hemangjoshi37a/SWiBoard/Capture2222.PNG

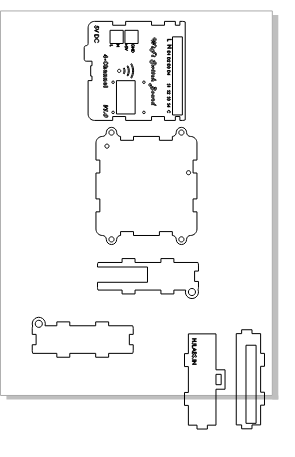
Capture2222.PNG
