hemangjoshi37a/SWiBoard/Capture.PNG

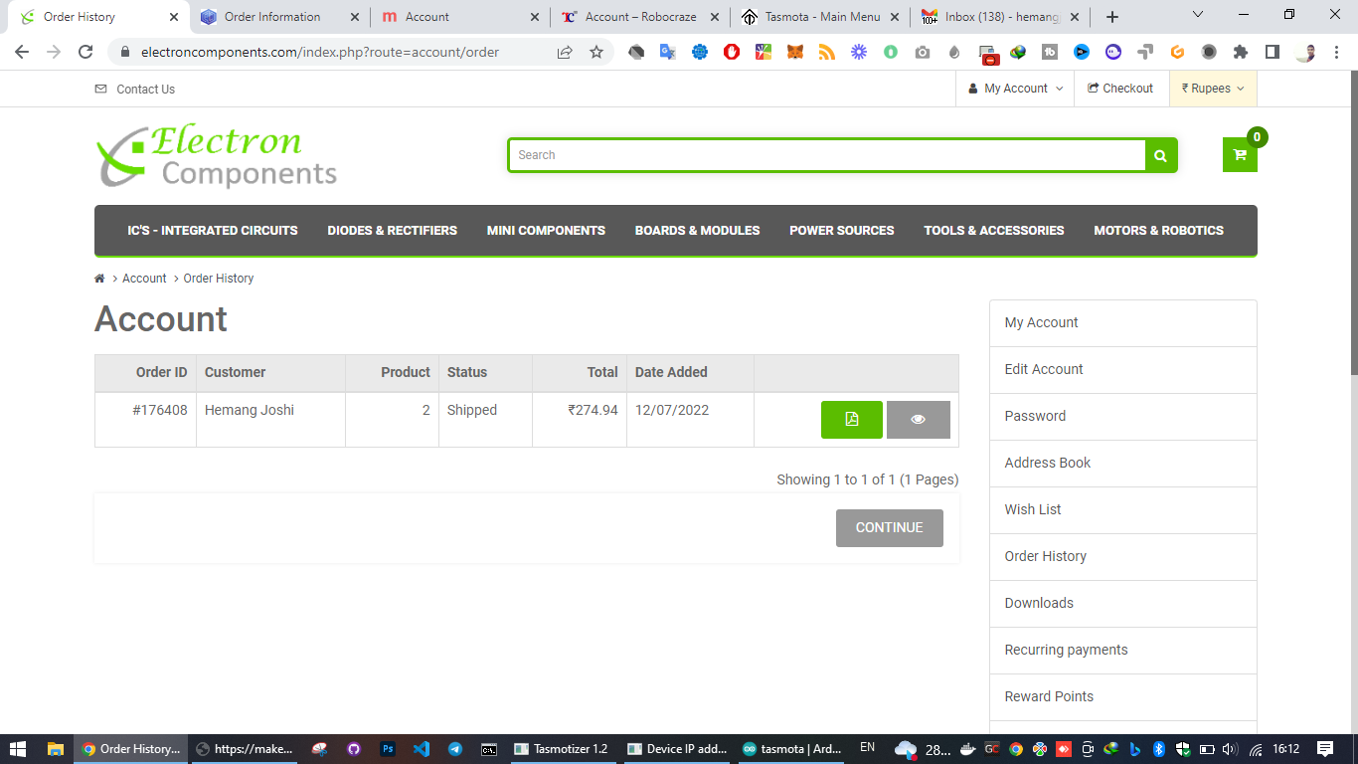
Capture.PNG
