hemangjoshi37a/SWiBoard/Cover_sticker_single.png

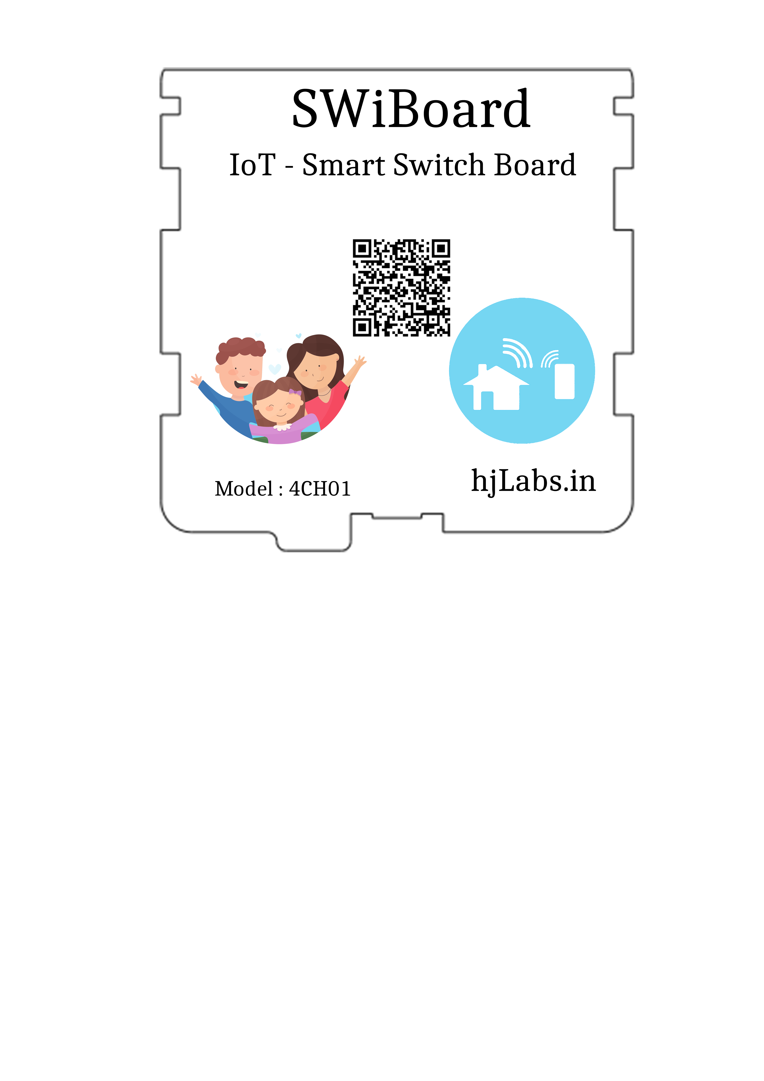
Cover_sticker_single.png
