hemangjoshi37a/SWiBoard/ESP12F_VS_ESP12E.jpg

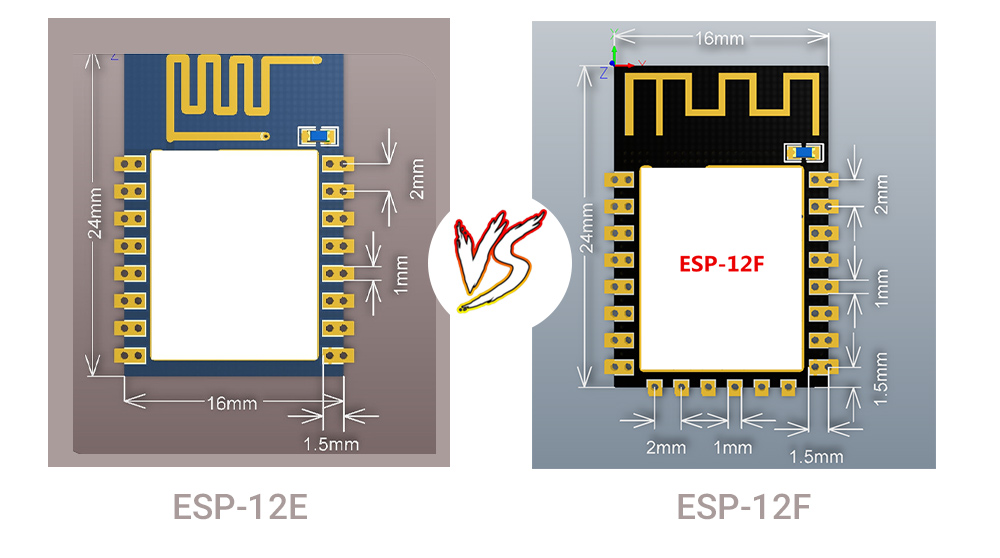
ESP12F_VS_ESP12E.jpg
