hemangjoshi37a/SWiBoard/esp8266_nodeMCU_wifi_switch_pcb_files/AC-Fan-Regulator-Control-Circuit.png

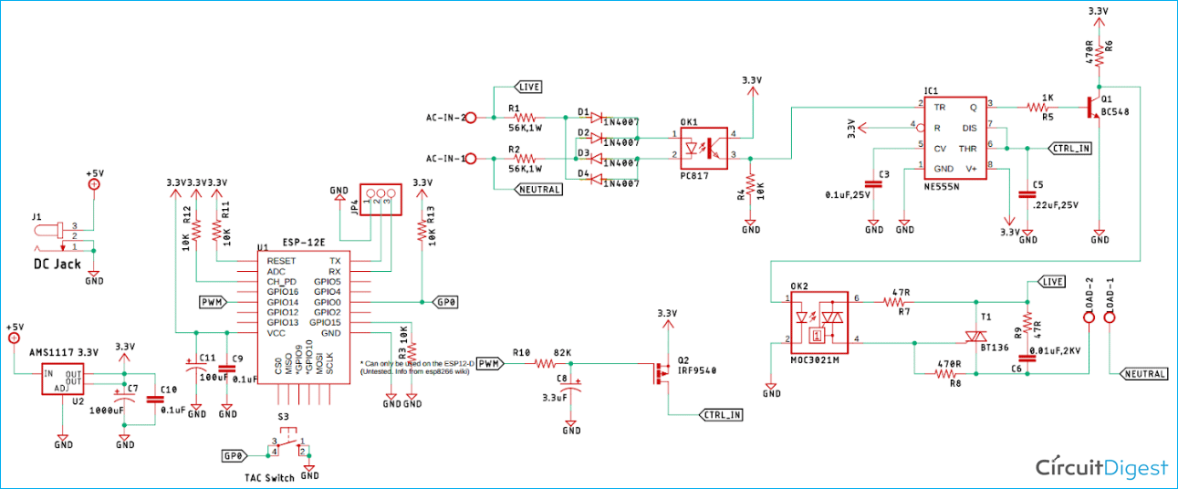
esp8266_nodeMCU_wifi_switch_pcb_files/AC-Fan-Regulator-Control-Circuit.png
