hemangjoshi37a/SWiBoard/flutter_android_app/google_play_dev_console_images/info_graphic_for_playstore.png

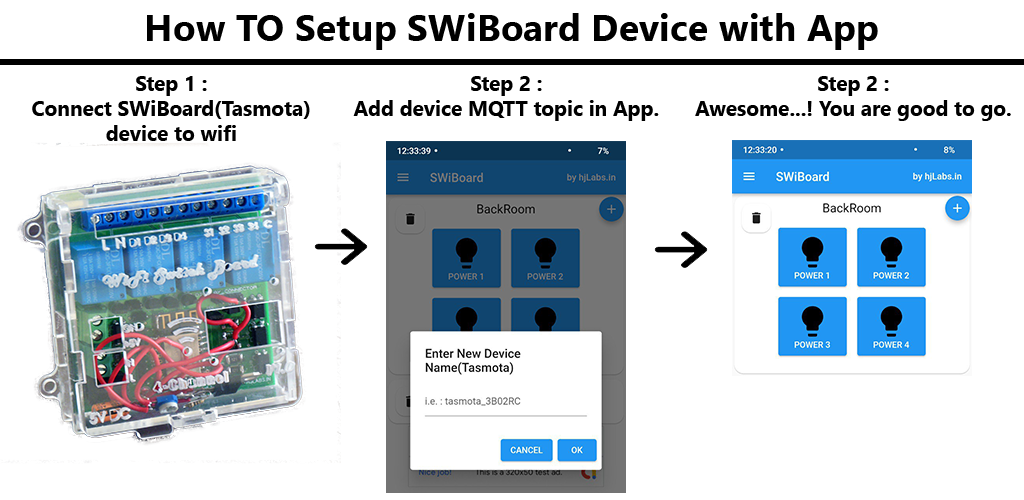
flutter_android_app/google_play_dev_console_images/info_graphic_for_playstore.png
