hemangjoshi37a/SWiBoard/flutter_android_app/google_play_dev_console_images/photo_2022-09-03_09-34-14.jpg

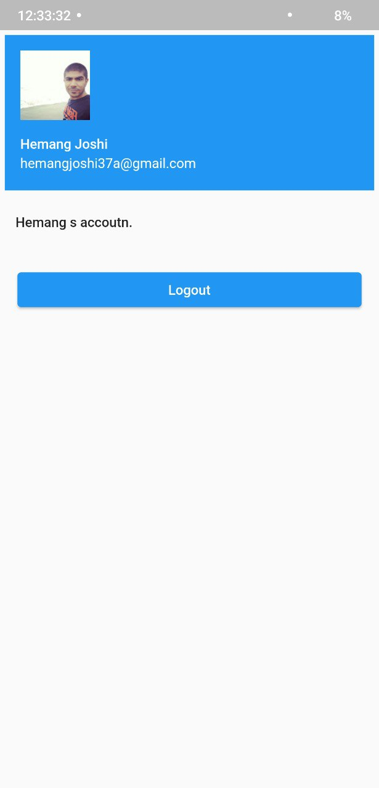
flutter_android_app/google_play_dev_console_images/photo_2022-09-03_09-34-14.jpg
