hemangjoshi37a/SWiBoard/flutter_android_app/google_play_dev_console_images/photo_2022-09-29_00-12-33.jpg

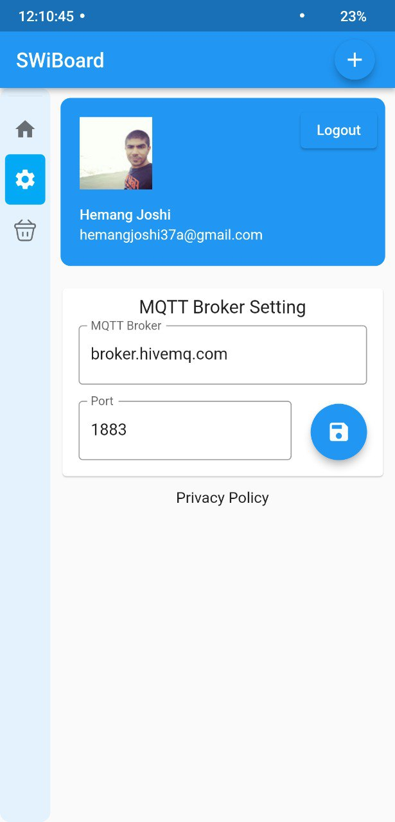
flutter_android_app/google_play_dev_console_images/photo_2022-09-29_00-12-33.jpg
