hemangjoshi37a/SWiBoard/flutter_android_app/google_play_dev_console_images/photo_2022-09-30_11-50-19.jpg

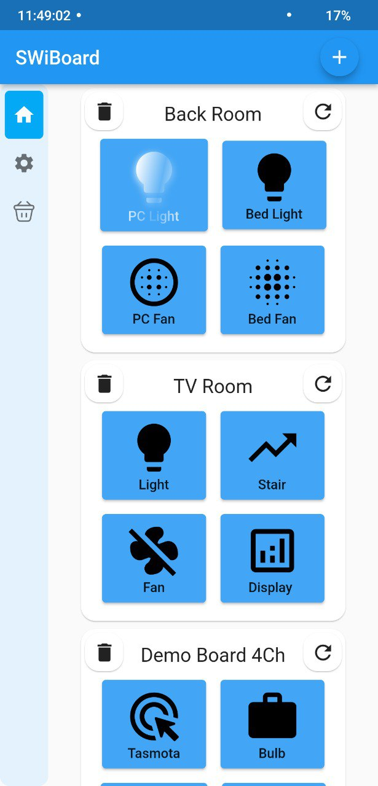
flutter_android_app/google_play_dev_console_images/photo_2022-09-30_11-50-19.jpg
