hemangjoshi37a/SWiBoard/flutter_android_app/google_play_dev_console_images/photo_2022-10-01_15-42-29.jpg

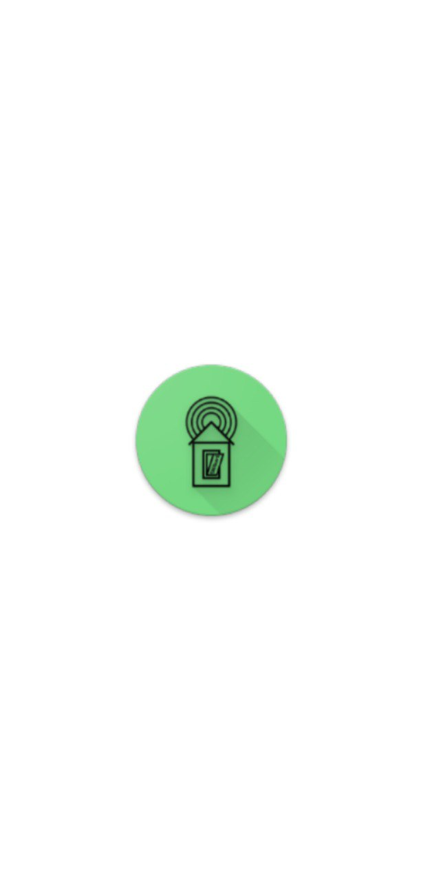
flutter_android_app/google_play_dev_console_images/photo_2022-10-01_15-42-29.jpg
