hemangjoshi37a/SWiBoard/flutter_android_app/google_play_dev_console_images/swiboard_screenshots_combined.png

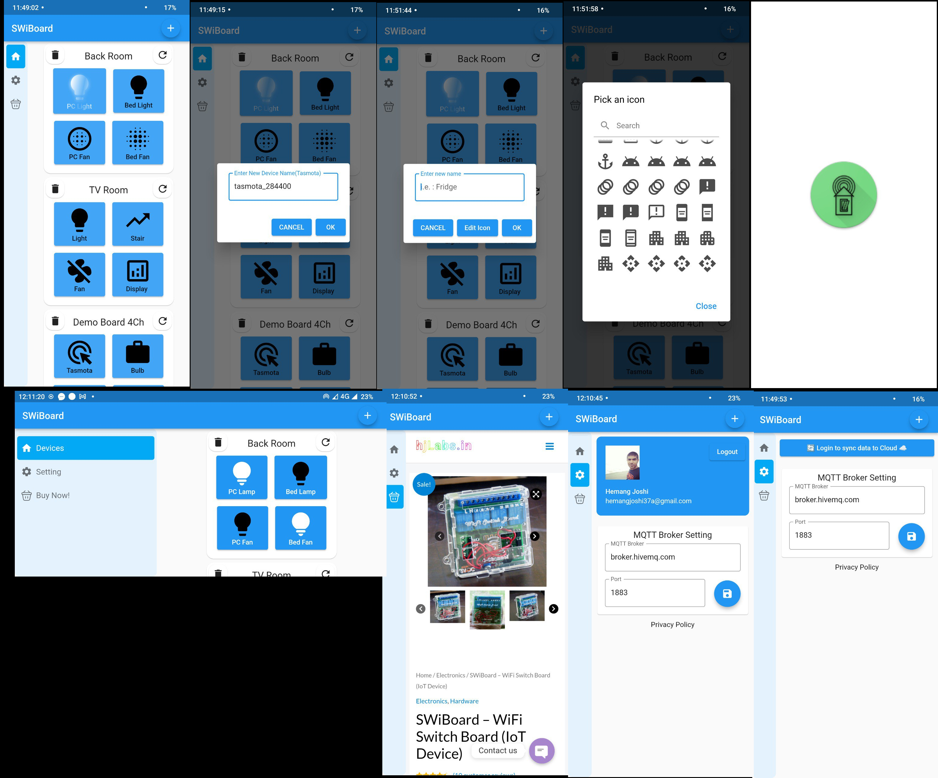
flutter_android_app/google_play_dev_console_images/swiboard_screenshots_combined.png
