hemangjoshi37a/SWiBoard/flutter_android_app/google_play_dev_console_images/tablet_screenshot_image.png

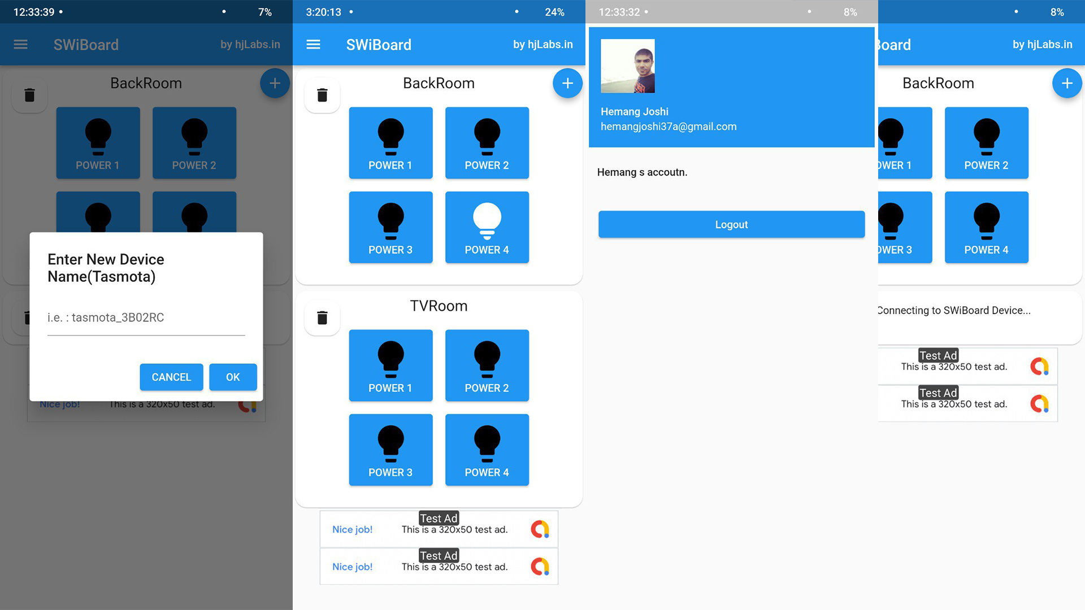
flutter_android_app/google_play_dev_console_images/tablet_screenshot_image.png
