hemangjoshi37a/SWiBoard/Nikon_camera_pics/DSCN5458.JPG

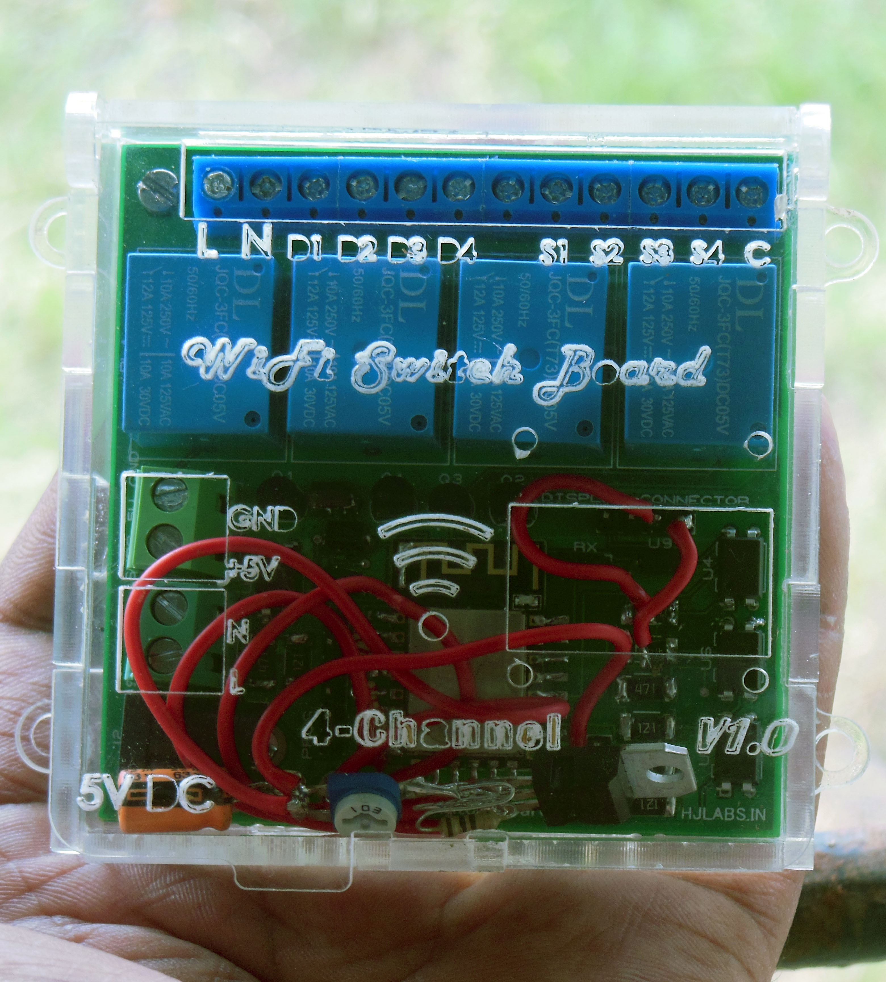
Nikon_camera_pics/DSCN5458.JPG
