hemangjoshi37a/SWiBoard/Nikon_camera_pics/DSCN5459.JPG

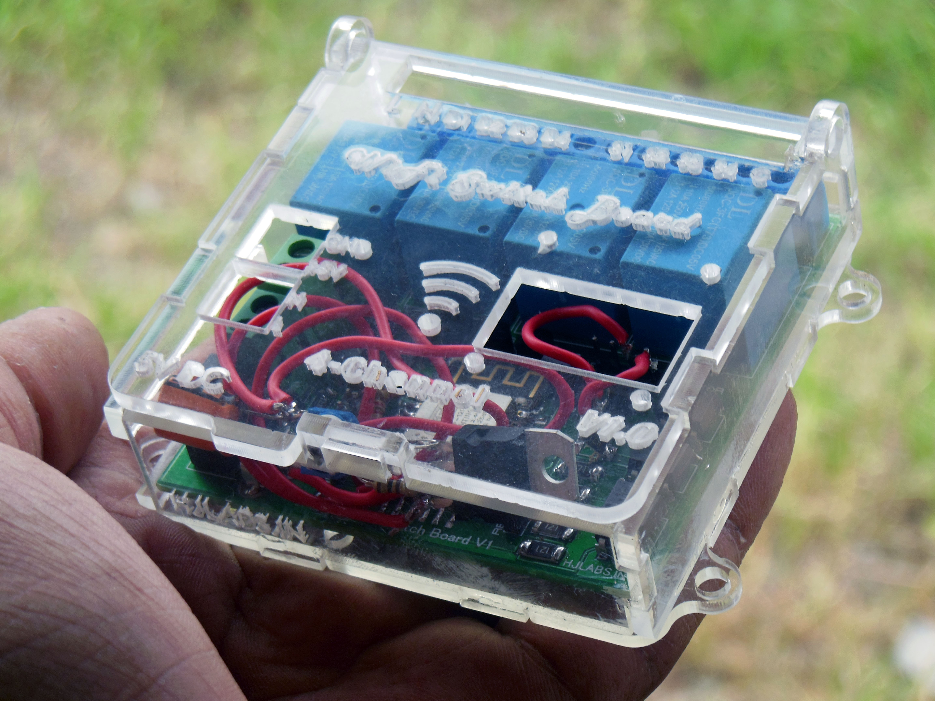
Nikon_camera_pics/DSCN5459.JPG
