hemangjoshi37a/SWiBoard/Nikon_camera_pics/DSCN5460.JPG

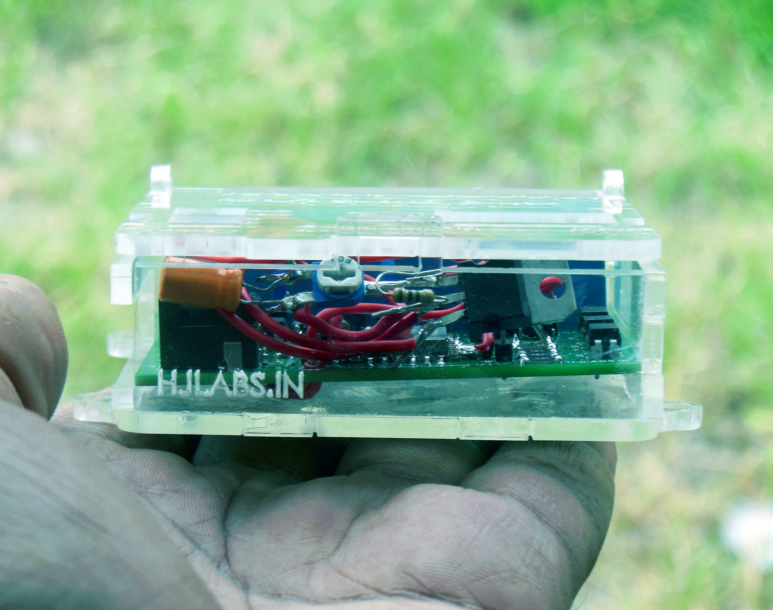
Nikon_camera_pics/DSCN5460.JPG
