hemangjoshi37a/SWiBoard/Nikon_camera_pics/DSCN5461.JPG

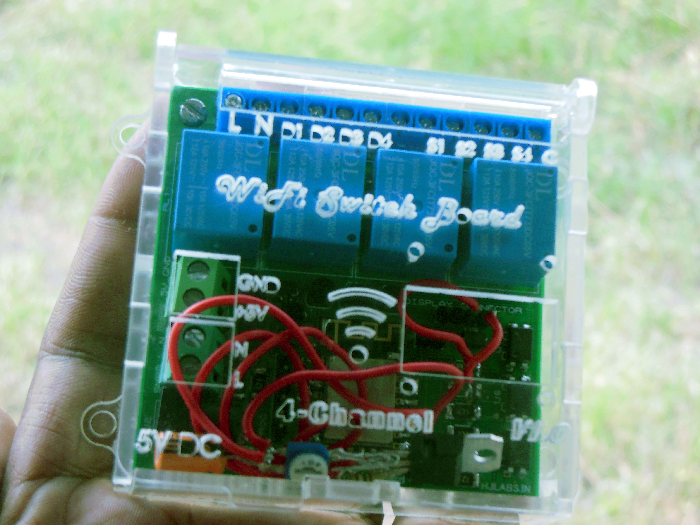
Nikon_camera_pics/DSCN5461.JPG
