hemangjoshi37a/SWiBoard/Nikon_camera_pics/DSCN5462.JPG

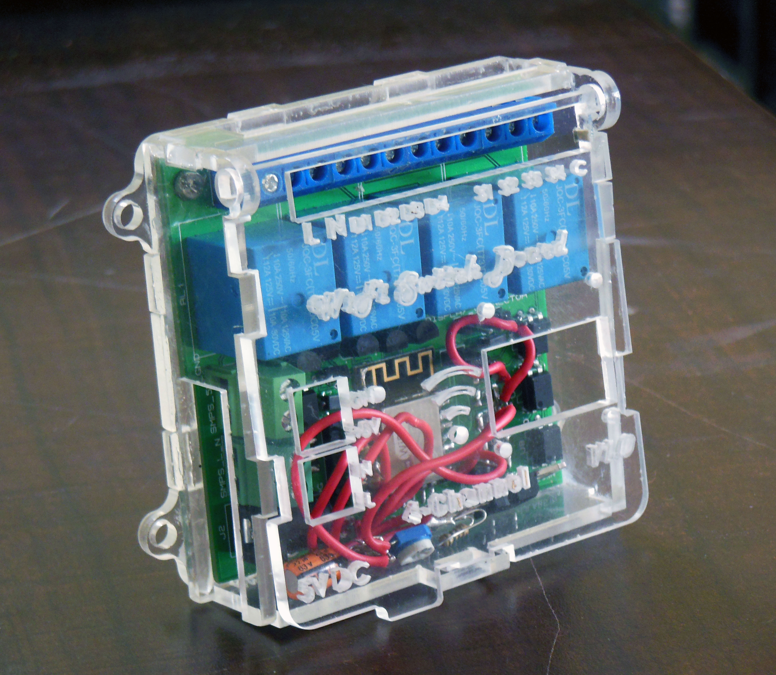
Nikon_camera_pics/DSCN5462.JPG
