hemangjoshi37a/SWiBoard/Nikon_camera_pics/DSCN5463.JPG

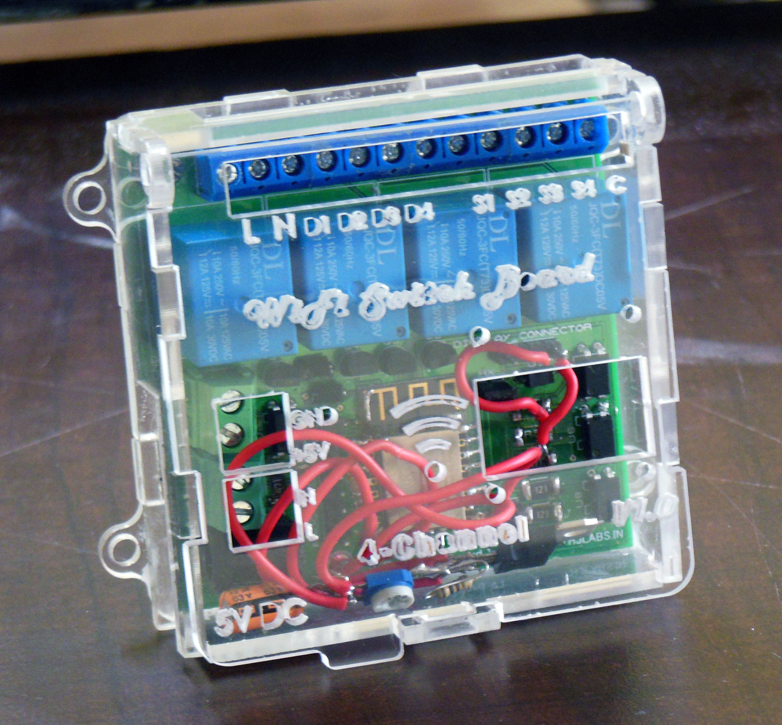
Nikon_camera_pics/DSCN5463.JPG
