hemangjoshi37a/SWiBoard/Nikon_camera_pics/photo_2022-08-03_13-36-46.jpg

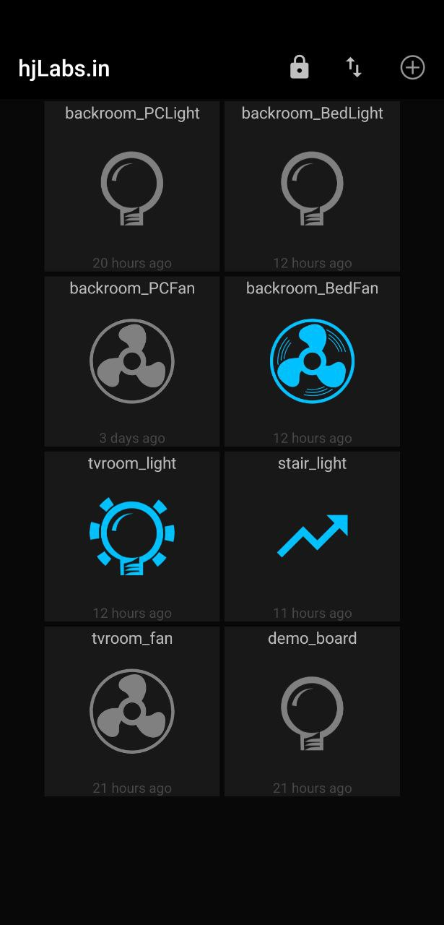
Nikon_camera_pics/photo_2022-08-03_13-36-46.jpg
