hemangjoshi37a/SWiBoard/PCB_FILES/BOX_CAD/render1.png

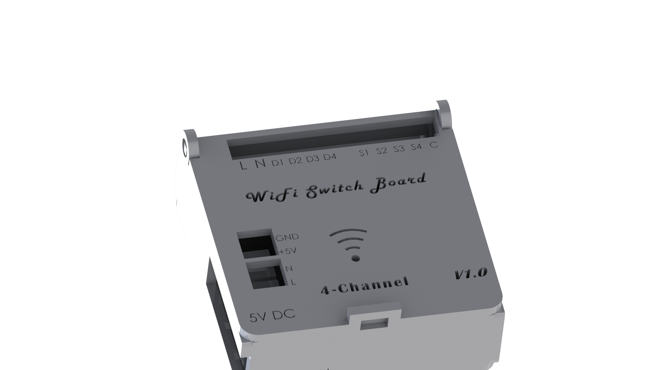
PCB_FILES/BOX_CAD/render1.png
