hemangjoshi37a/SWiBoard/PCB_FILES/BOX_CAD/render2.png

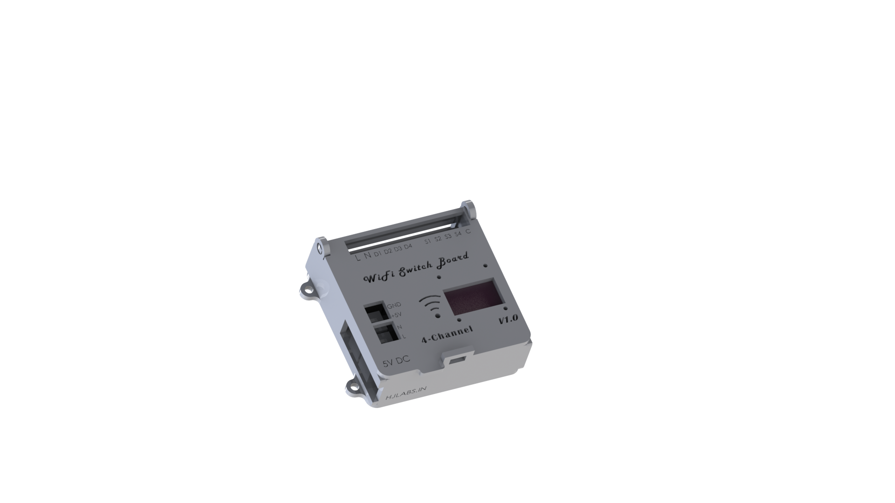
PCB_FILES/BOX_CAD/render2.png
