hemangjoshi37a/SWiBoard/terminal-block-12-positions-dual-rows-covered-600v-15a-configurable-1.snapshot.2/Terminal Block, 12 Positions, Dual Rows Covered, 600V 15A , Configurable.JPG

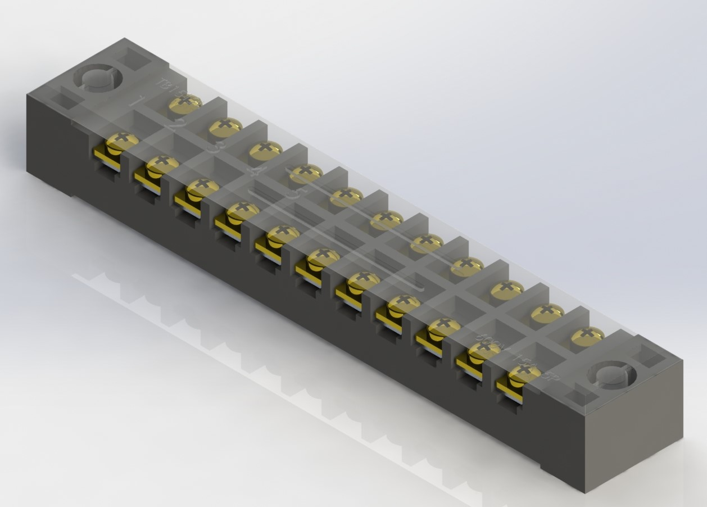
terminal-block-12-positions-dual-rows-covered-600v-15a-configurable-1.snapshot.2/Terminal Block, 12 Positions, Dual Rows Covered, 600V 15A , Configurable.JPG
