hemangjoshi37a/SWiBoard/ULN2803_with_opto_PC817_relay_driver_circuit.PNG

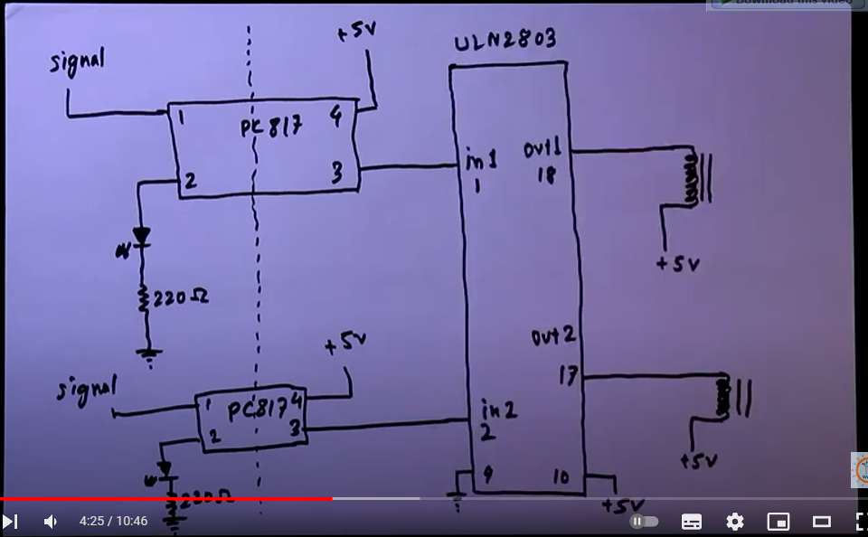
ULN2803_with_opto_PC817_relay_driver_circuit.PNG
