hemangjoshi37a/SWiBoard/terminal-block-12-positions-dual-rows-covered-600v-15a-configurable-1.snapshot.2/Cover, Terminal Block, 12 Positions, Dual Rows Covered, 600V 15A , Configurable.SLDPRT

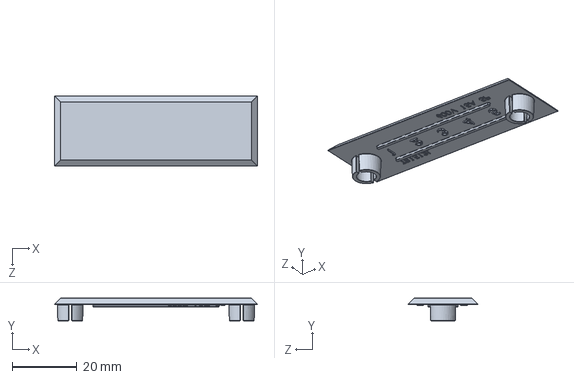
[picture p52: CAD file, 2023-01-12]
terminal-block-12-positions-dual-rows-covered-600v-15a-configurable-1.snapshot.2/Cover, Terminal Block, 12 Positions, Dual Rows Covered, 600V 15A , Configurable.SLDPRT
62.7 x 7.00 x 21.7 mm
