hemangjoshi37a/SWiBoard/4-channel-relay-module-5v-no-name-1.snapshot.2/4 Channel No Name Relay Parts/4 Ch - 5v Relay Board.SLDPRT

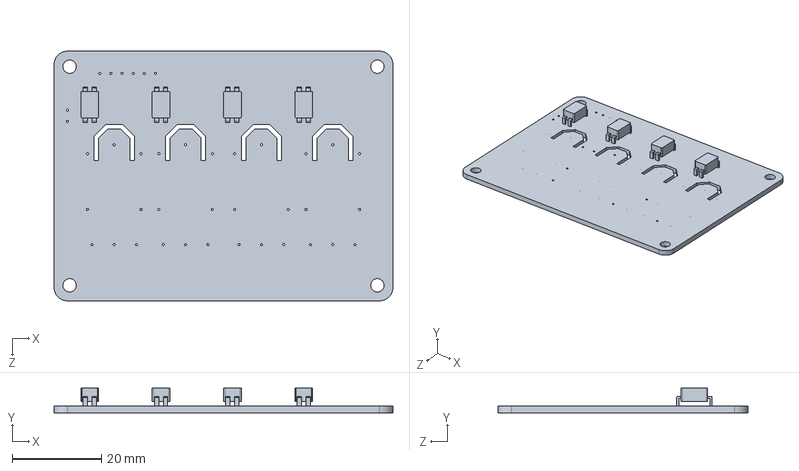
[picture p53: CAD file, 2023-01-12]
4-channel-relay-module-5v-no-name-1.snapshot.2/4 Channel No Name Relay Parts/4 Ch - 5v Relay Board.SLDPRT
76.0 x 5.50 x 56.0 mm
