hemangjoshi37a/SWiBoard/switch.SLDPRT

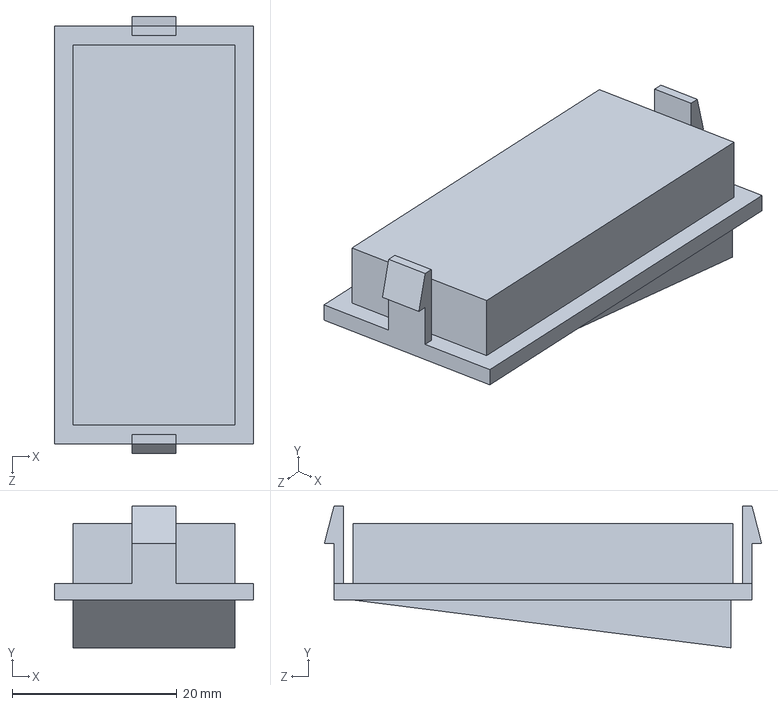
[picture p54: CAD file, 2023-01-12]
switch.SLDPRT
24.1 x 17.2 x 53.0 mm
