hemangjoshi37a/SWiBoard/terminal-block-12-positions-dual-rows-covered-600v-15a-configurable-1.snapshot.2/Terminal Block, 12 Positions, Dual Rows Covered, 600V 15A , Configurable.STEP

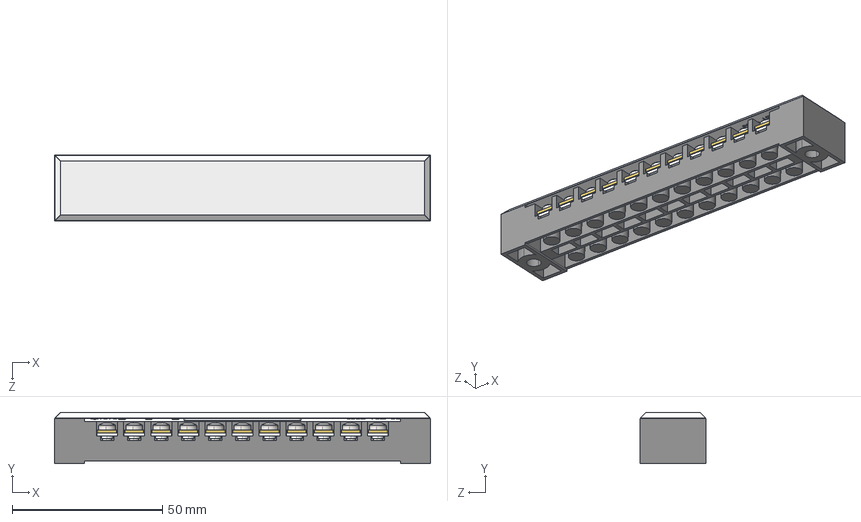
[picture p55: CAD file, 2023-01-12]
terminal-block-12-positions-dual-rows-covered-600v-15a-configurable-1.snapshot.2/Terminal Block, 12 Positions, Dual Rows Covered, 600V 15A , Configurable.STEP
125.0 x 17.0 x 22.0 mm
Block, Terminal Block, 12 Positions, Dual Rows Covered, 600V 15A , Configurable
Conducting Strip, Terminal Block, 12 Positions, Dual Rows Covered, 600V 15A , Configurable x 11
Cover, Terminal Block, 12 Positions, Dual Rows Covered, 600V 15A , Configurable
Terminal Plate, Terminal Block, 12 Positions, Dual Rows Covered, 600V 15A , Configurable x 22
pan cross head_am_B18.6.7M - M3 x 0.5 x 6 Type I Cross Recessed PHMS --6N x 22
