hemangjoshi37a/SWiBoard/PCB_FILES_V2/BOX_CAD/top_plate2.SLDPRT

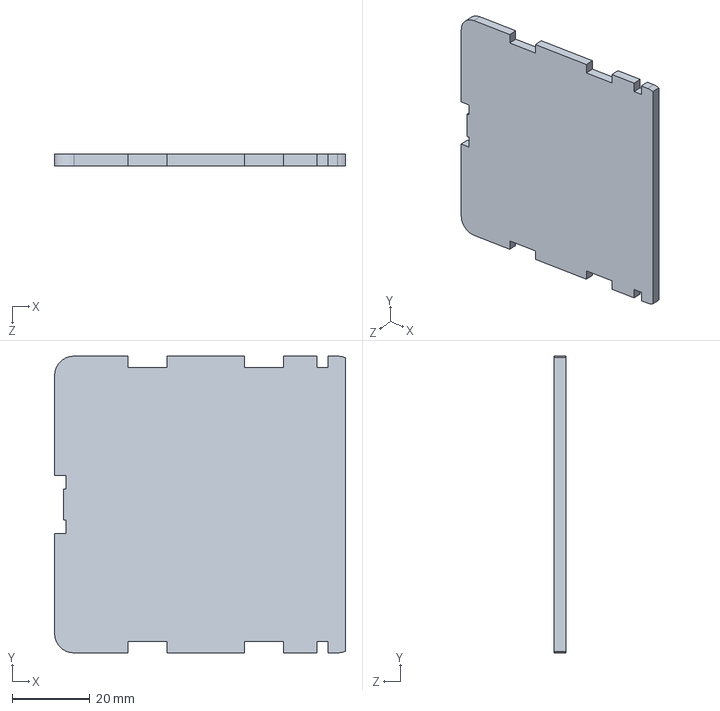
[picture p57: CAD file, 2023-01-12]
PCB_FILES_V2/BOX_CAD/top_plate2.SLDPRT
75.0 x 76.5 x 3.00 mm
