hemangjoshi37a/SWiBoard/terminal-block-12-positions-dual-rows-covered-600v-15a-configurable-1.snapshot.2/Terminal Plate, Terminal Block, 12 Positions, Dual Rows Covered, 600V 15A , Configurable.SLDPRT

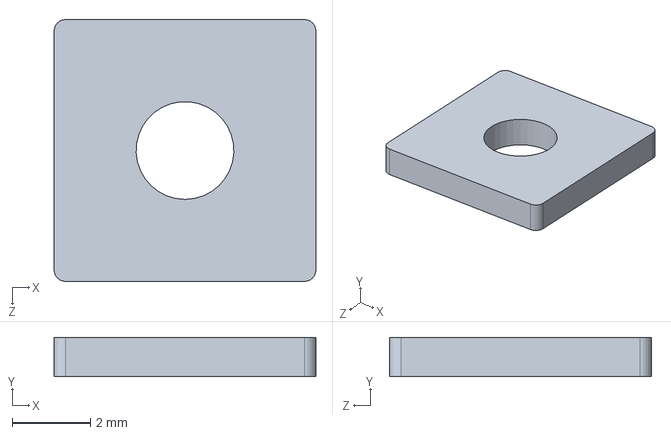
[picture p58: CAD file, 2023-01-12]
terminal-block-12-positions-dual-rows-covered-600v-15a-configurable-1.snapshot.2/Terminal Plate, Terminal Block, 12 Positions, Dual Rows Covered, 600V 15A , Configurable.SLDPRT
6.70 x 1.00 x 6.70 mm
