hemangjoshi37a/SWiBoard/4-channel-relay-module-5v-no-name-1.snapshot.2/4 Channel No Name Relay Parts/6 Header.SLDPRT

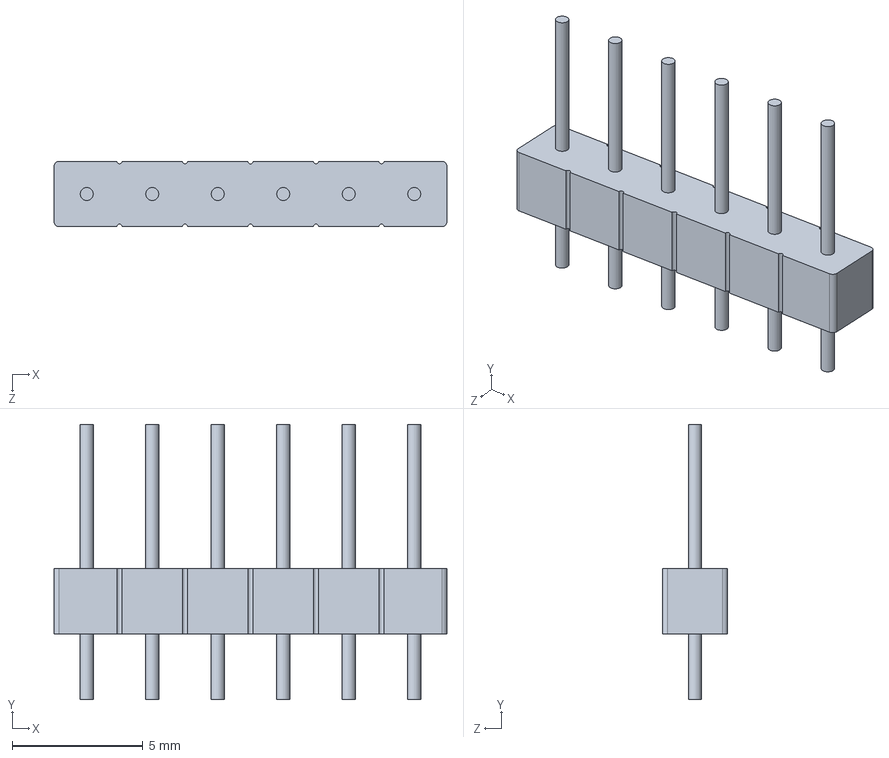
[picture p59: CAD file, 2023-01-12]
4-channel-relay-module-5v-no-name-1.snapshot.2/4 Channel No Name Relay Parts/6 Header.SLDPRT
15.0 x 10.5 x 2.50 mm
