hemangjoshi37a/SWiBoard/back_plate.SLDPRT

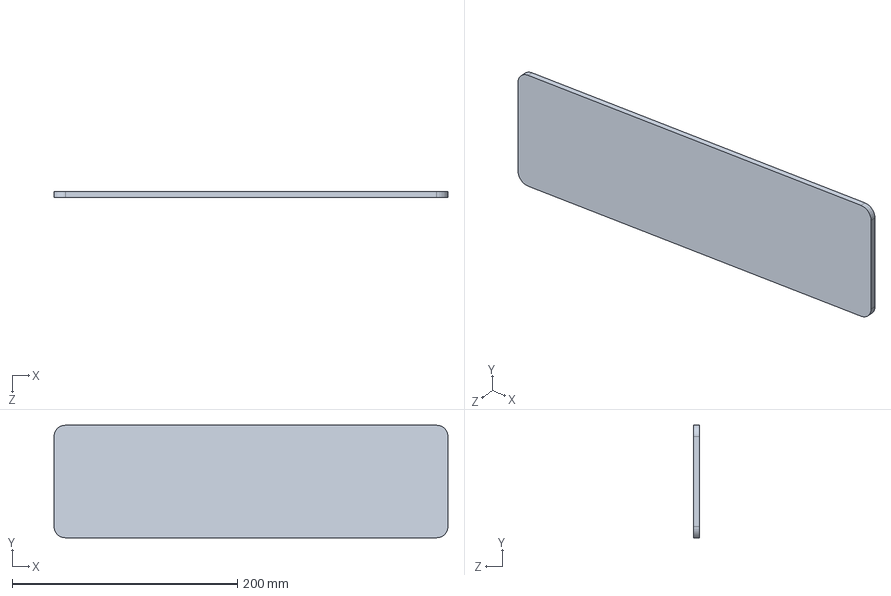
[picture p60: CAD file, 2023-01-12]
back_plate.SLDPRT
350.0 x 100.0 x 5.00 mm
