hemangjoshi37a/SWiBoard/PCB_FILES_V2/BOX_CAD/top_plate.SLDPRT

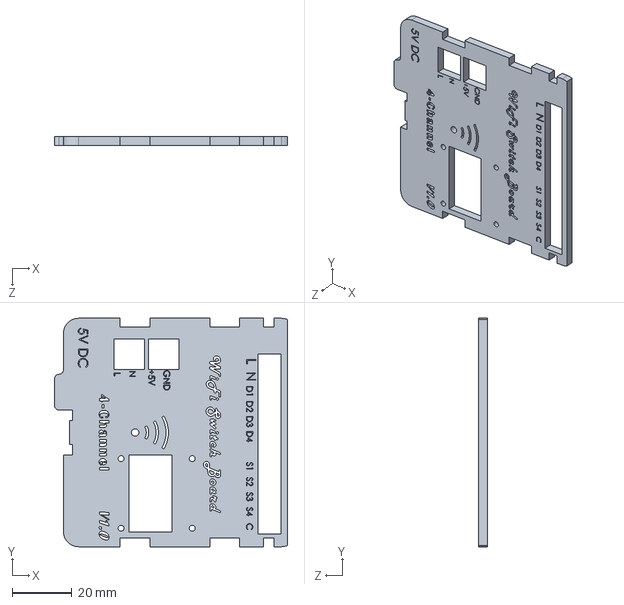
[picture p61: CAD file, 2023-01-12]
PCB_FILES_V2/BOX_CAD/top_plate.SLDPRT
78.0 x 76.5 x 3.00 mm
