hemangjoshi37a/SWiBoard/terminal-block-12-positions-dual-rows-covered-600v-15a-configurable-1.snapshot.2/Block, Terminal Block, 12 Positions, Dual Rows Covered, 600V 15A , Configurable.SLDPRT

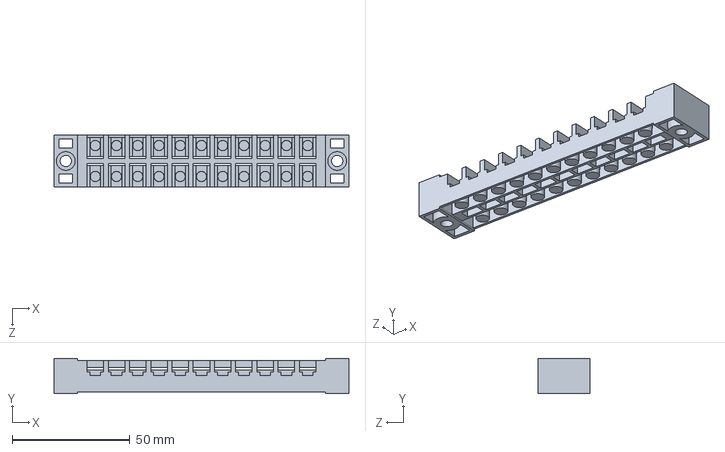
[picture p62: CAD file, 2023-01-12]
terminal-block-12-positions-dual-rows-covered-600v-15a-configurable-1.snapshot.2/Block, Terminal Block, 12 Positions, Dual Rows Covered, 600V 15A , Configurable.SLDPRT
125.0 x 15.0 x 22.0 mm
