hemangjoshi37a/SWiBoard/plug_socket.SLDPRT

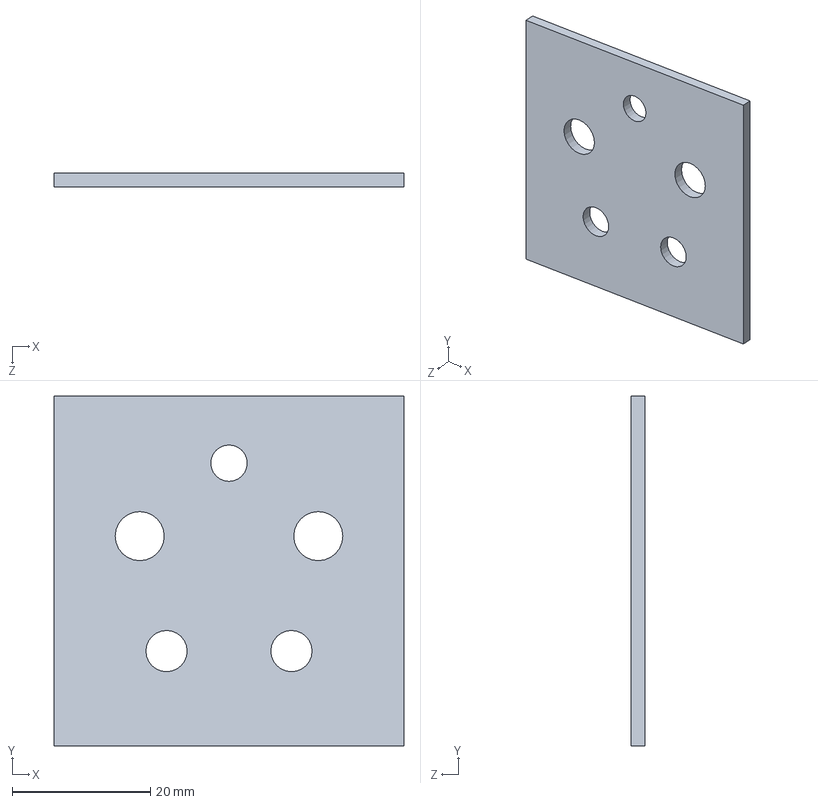
[picture p64: CAD file, 2023-01-12]
plug_socket.SLDPRT
50.7 x 50.7 x 2.00 mm
