hemangjoshi37a/SWiBoard/4-channel-relay-module-5v-no-name-1.snapshot.2/4 Channel No Name Relay Parts/Relay Body.SLDPRT

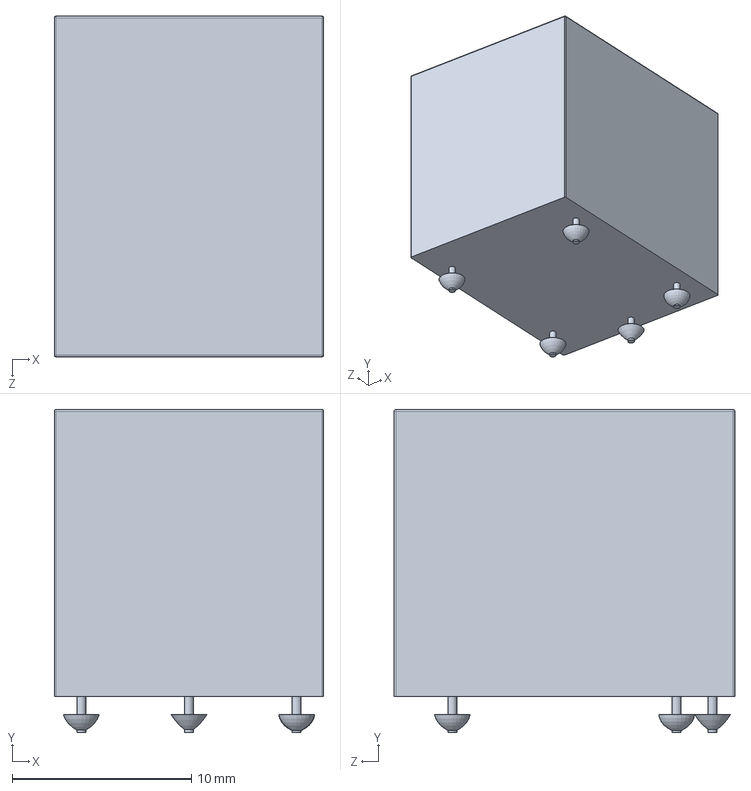
[picture p66: CAD file, 2023-01-12]
4-channel-relay-module-5v-no-name-1.snapshot.2/4 Channel No Name Relay Parts/Relay Body.SLDPRT
15.0 x 18.0 x 19.0 mm
