hemangjoshi37a/SWiBoard/wiring_diagram.png

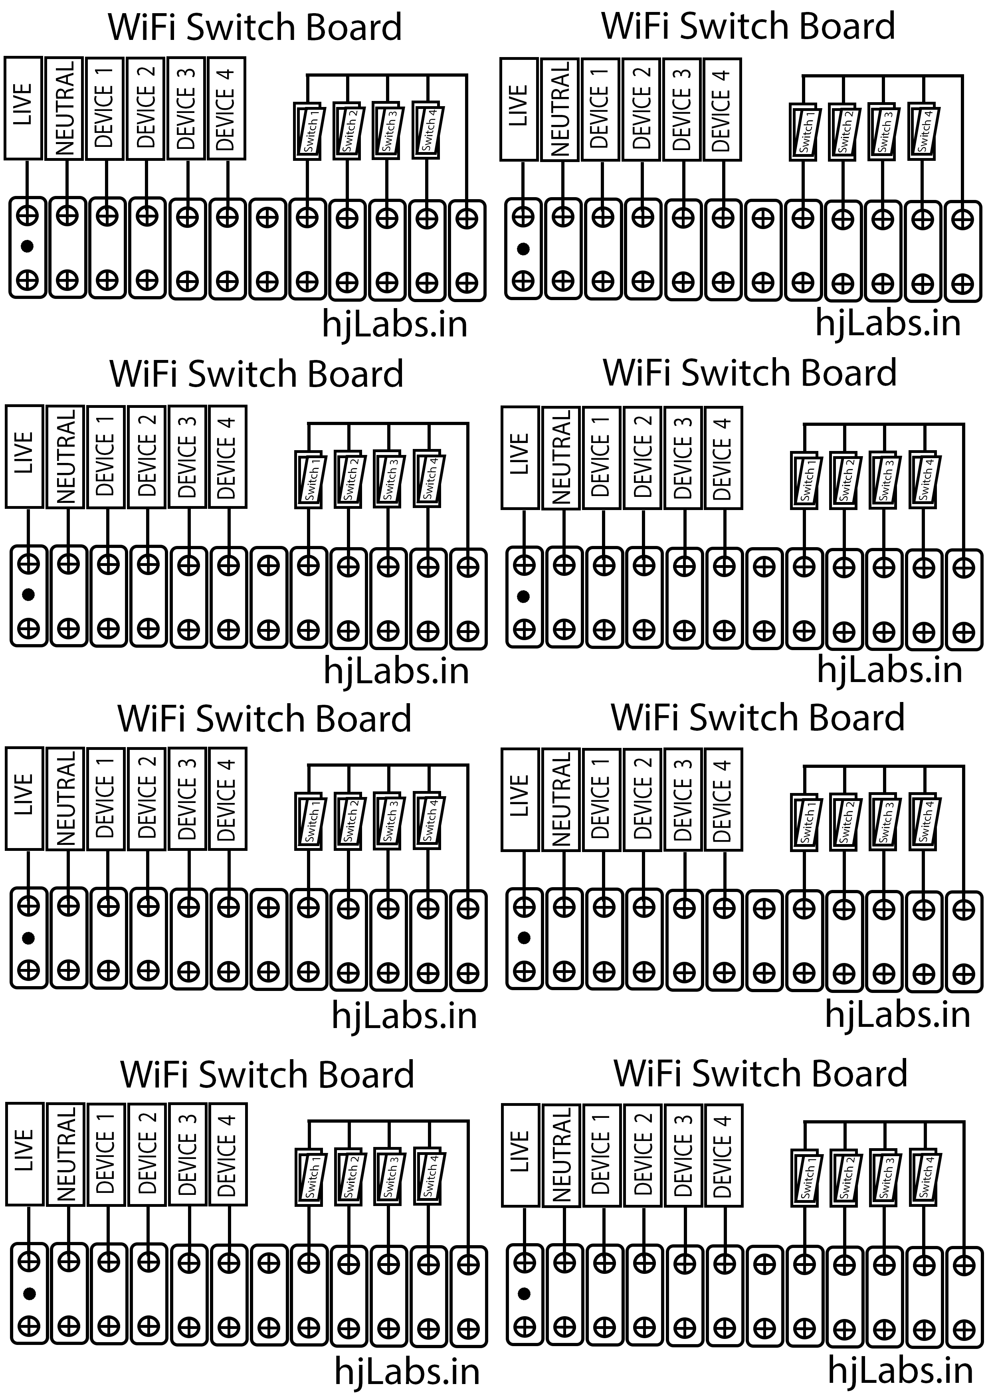
wiring_diagram.png
