hemangjoshi37a/SWiBoard/wiring_diagram_inside_box.png

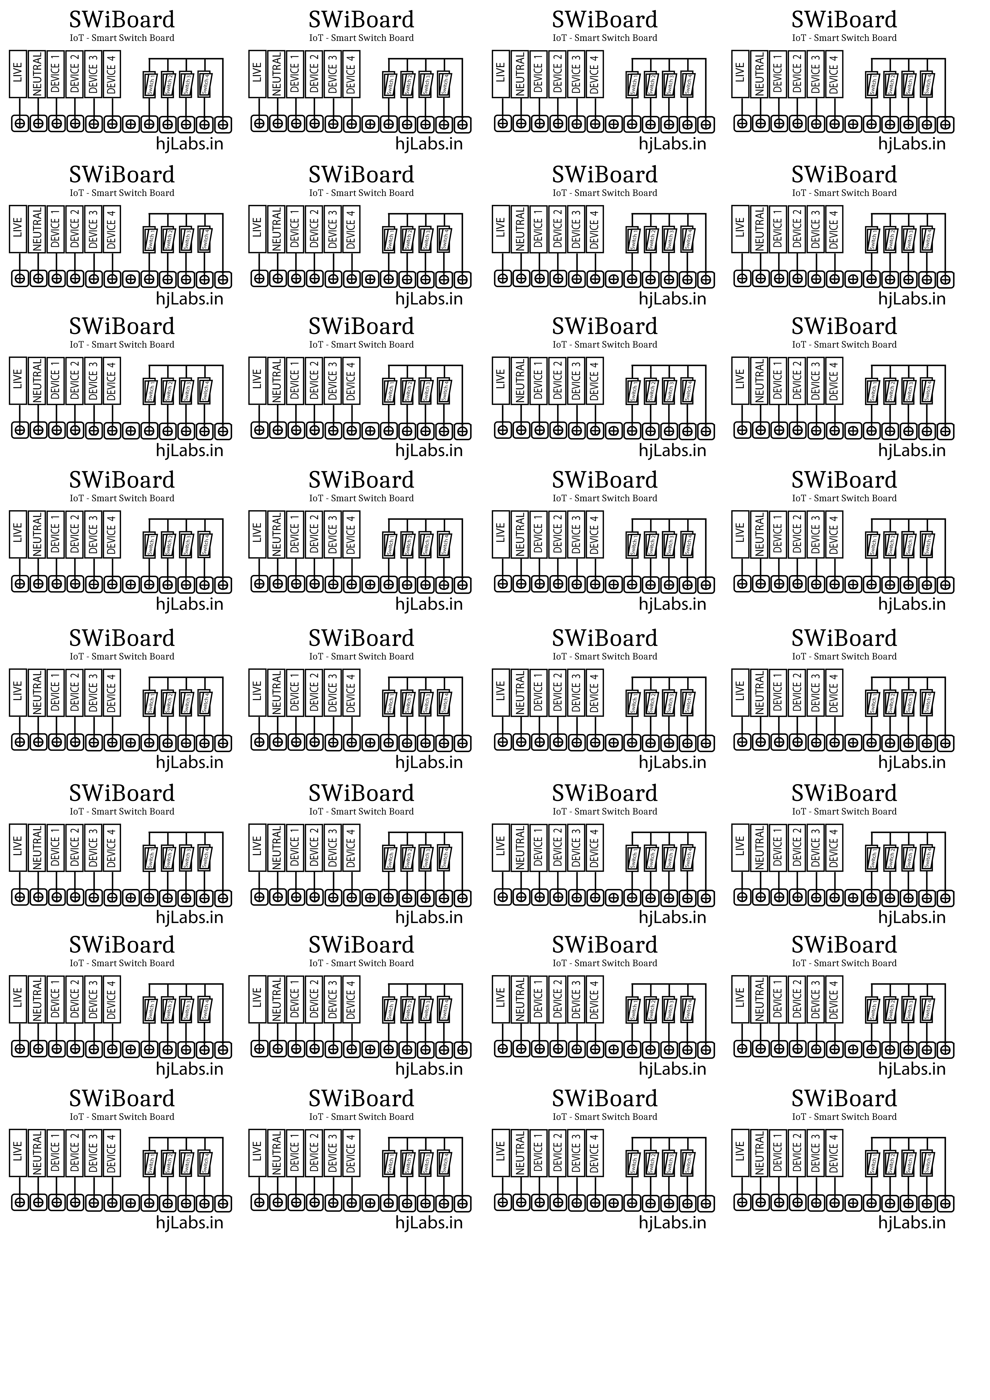
wiring_diagram_inside_box.png
