hemangjoshi37a/SWiBoard/wiring_diagram_simgle.png

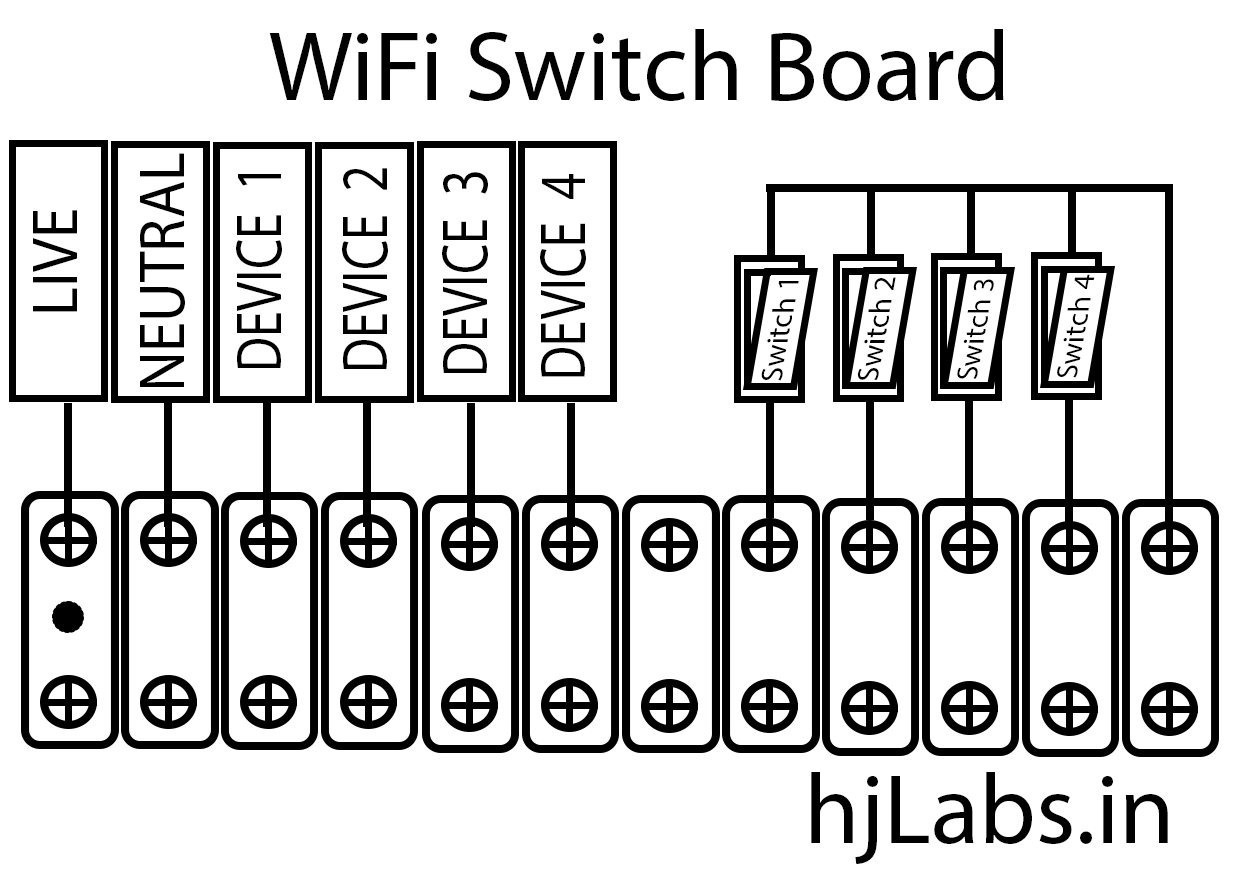
wiring_diagram_simgle.png
